gocivici/trinteract/docs/_images/schema.png

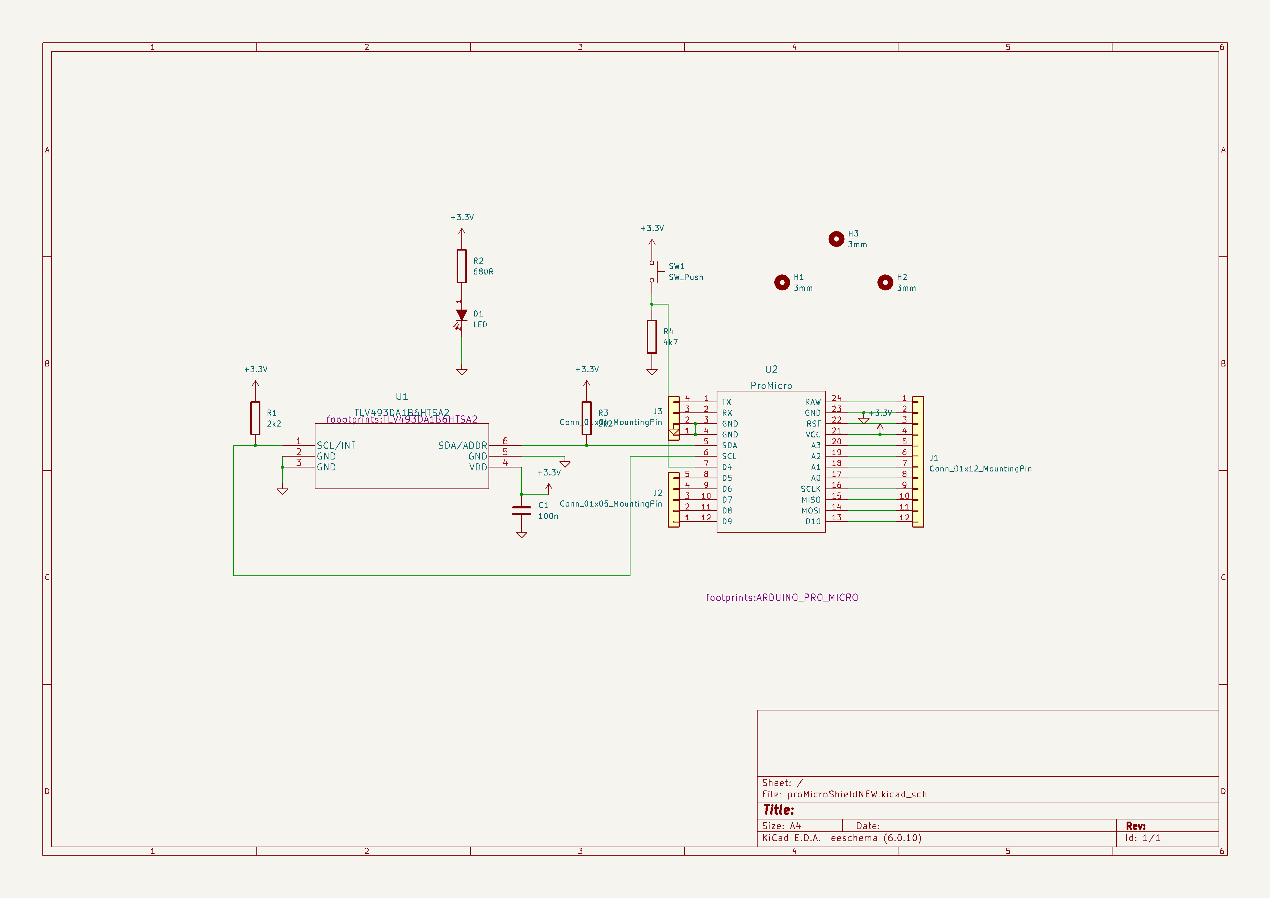
docs/_images/schema.png
