gocivici/trinteract/media/trinteract.gif

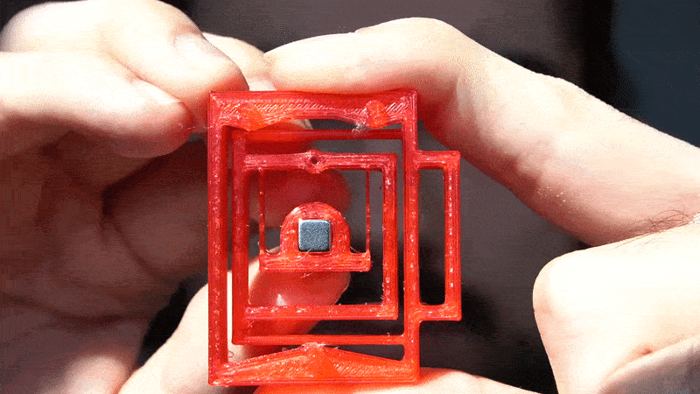
media/trinteract.gif
