gocivici/trinteract/docs/_images/wiring.png

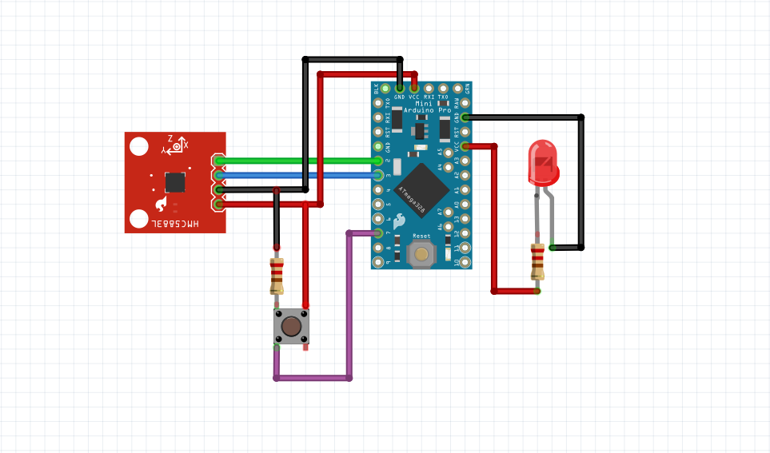
docs/_images/wiring.png
