gocivici/trinteract/docs/source/build_your_own/3D2.jpg

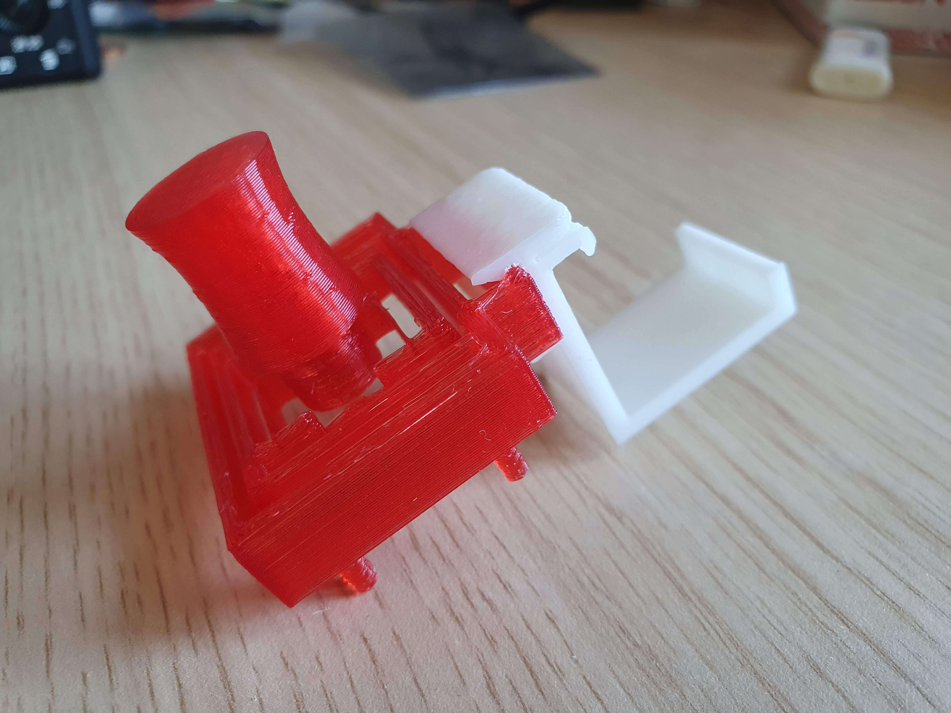
docs/source/build_your_own/3D2.jpg
