gocivici/trinteract/docs/source/build_your_own/3D.jpg

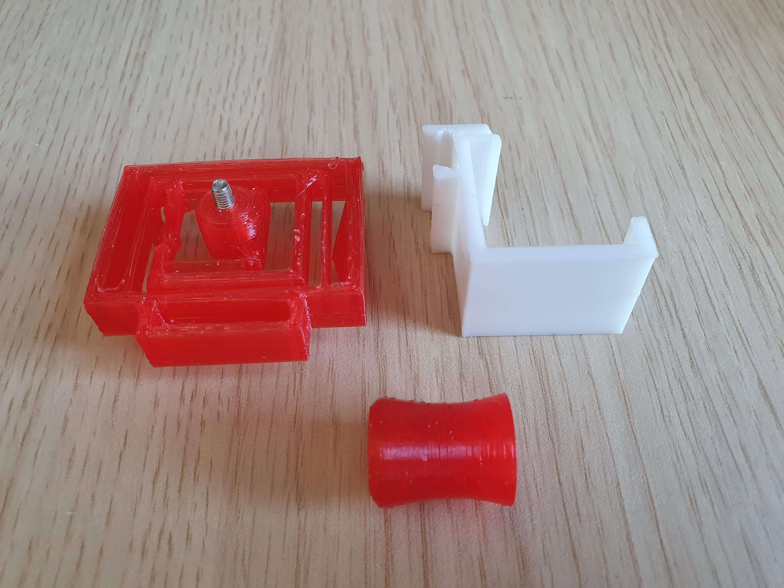
docs/source/build_your_own/3D.jpg
